pradyjowski/aquaduino/IMG_3391.JPG

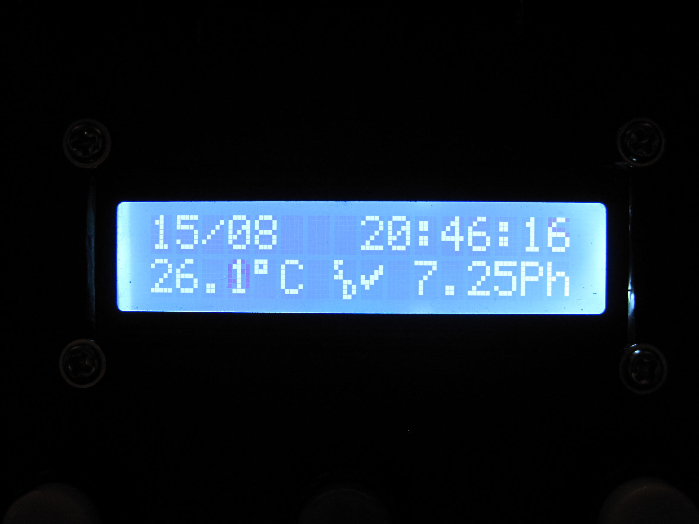
IMG_3391.JPG
